Julian-Baumeler/marmot/website/figures/emb-036.png

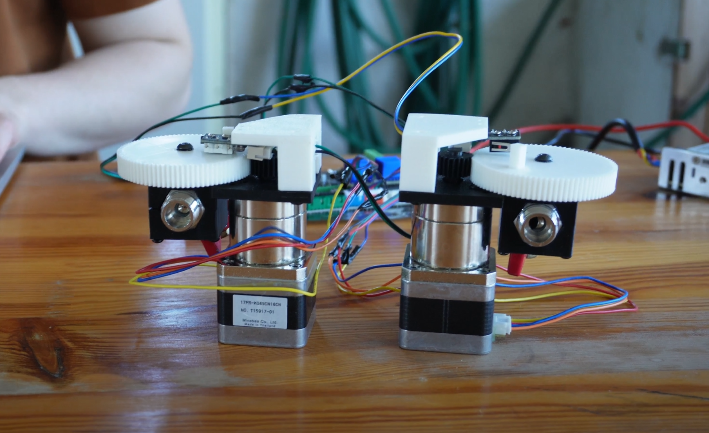
website/figures/emb-036.png
