Julian-Baumeler/marmot/website/figures/emb-038.png

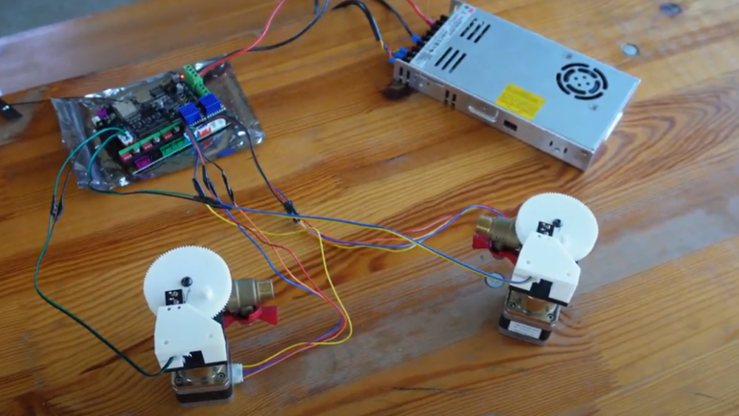
website/figures/emb-038.png
