Julian-Baumeler/marmot/website/figures/emb-051.png

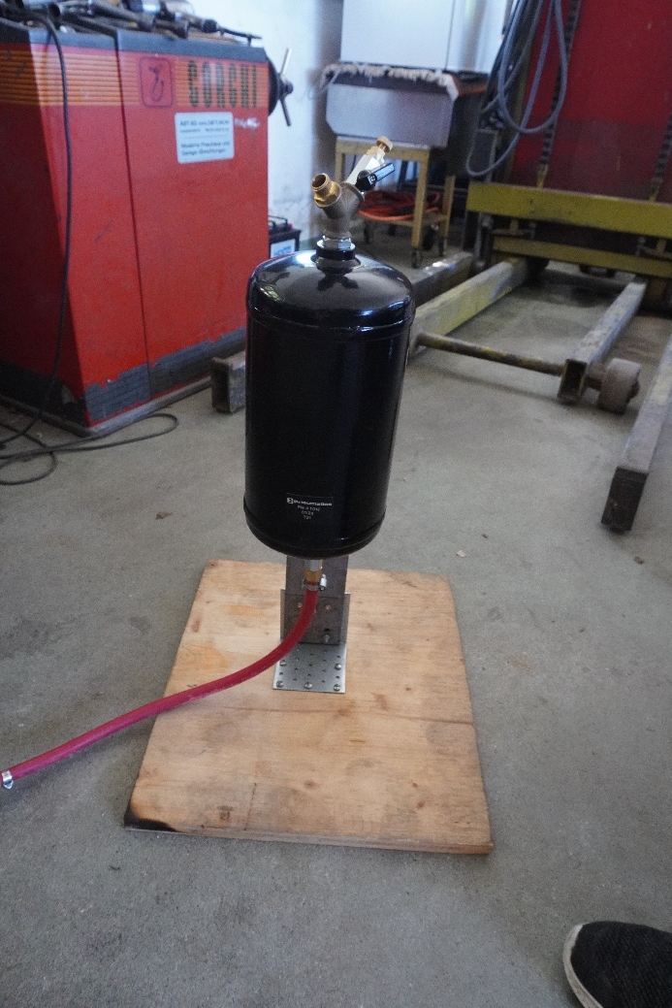
website/figures/emb-051.png
