Julian-Baumeler/marmot/website/models/Engine2-preview.png

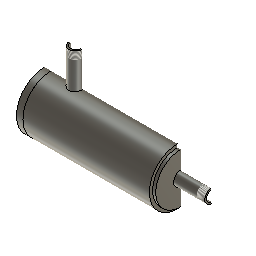
website/models/Engine2-preview.png
