Julian-Baumeler/marmot/website/models/Engine-preview.png

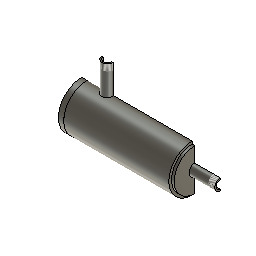
website/models/Engine-preview.png
