Julian-Baumeler/marmot/website/posters/06-mf-6.jpg

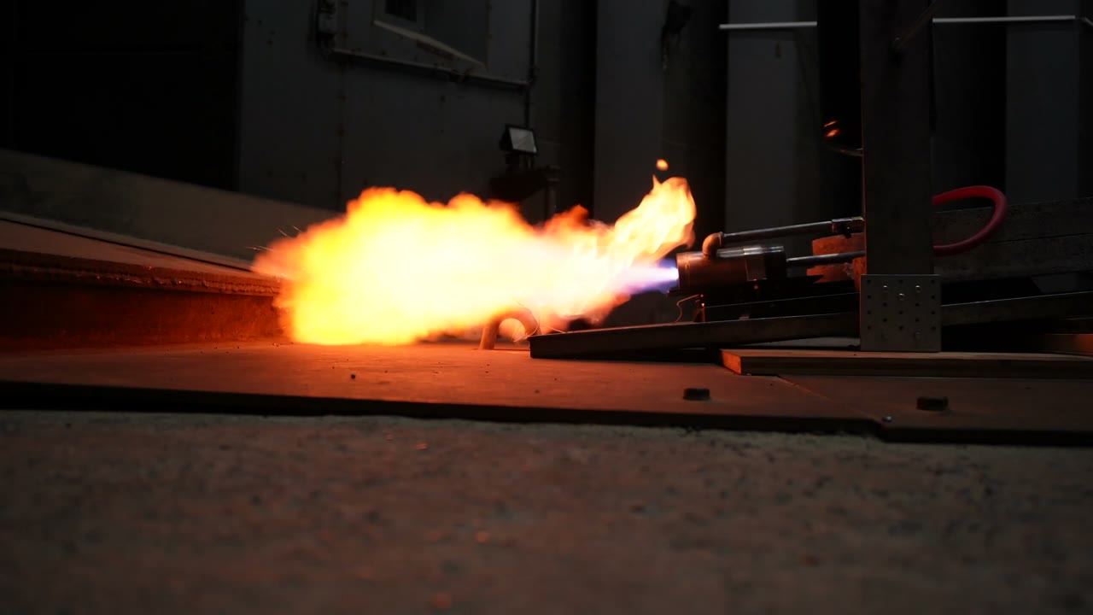
website/posters/06-mf-6.jpg
