Julian-Baumeler/marmot/website/posters/06-mf-6a.jpg

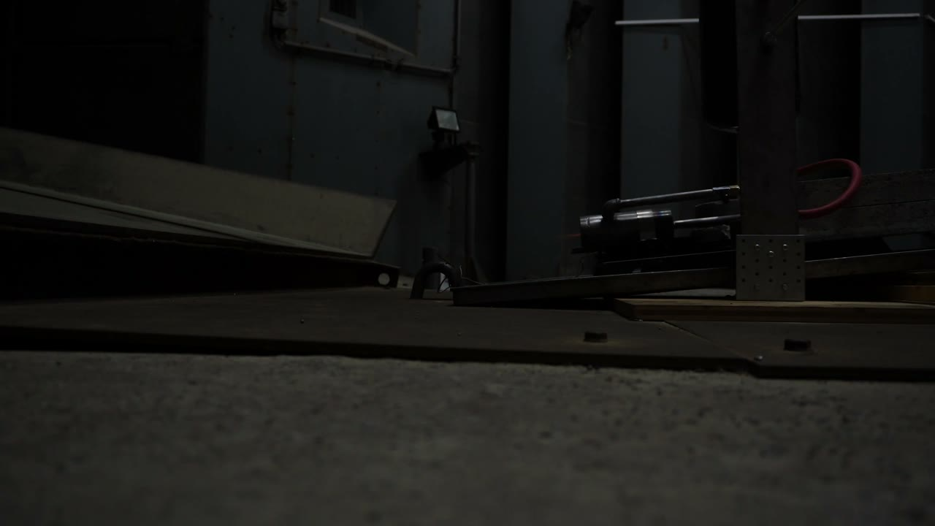
website/posters/06-mf-6a.jpg
