Julian-Baumeler/marmot/website/posters/06-mf-6b.jpg

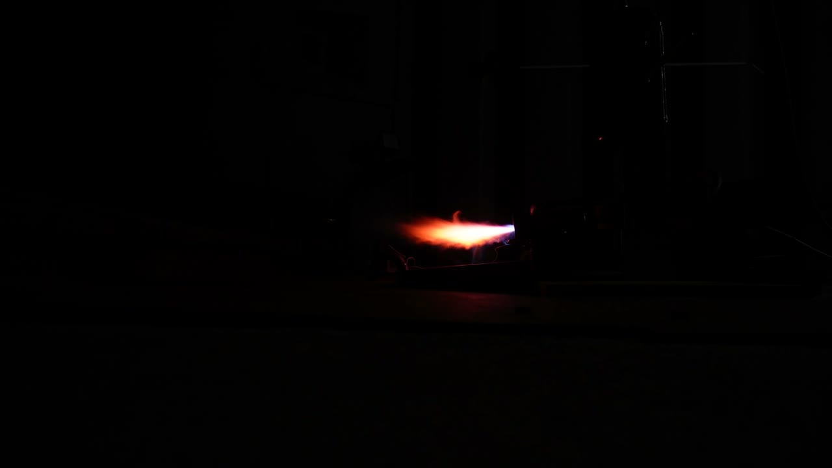
website/posters/06-mf-6b.jpg
