Julian-Baumeler/marmot/website/posters/06-mf-6c.jpg

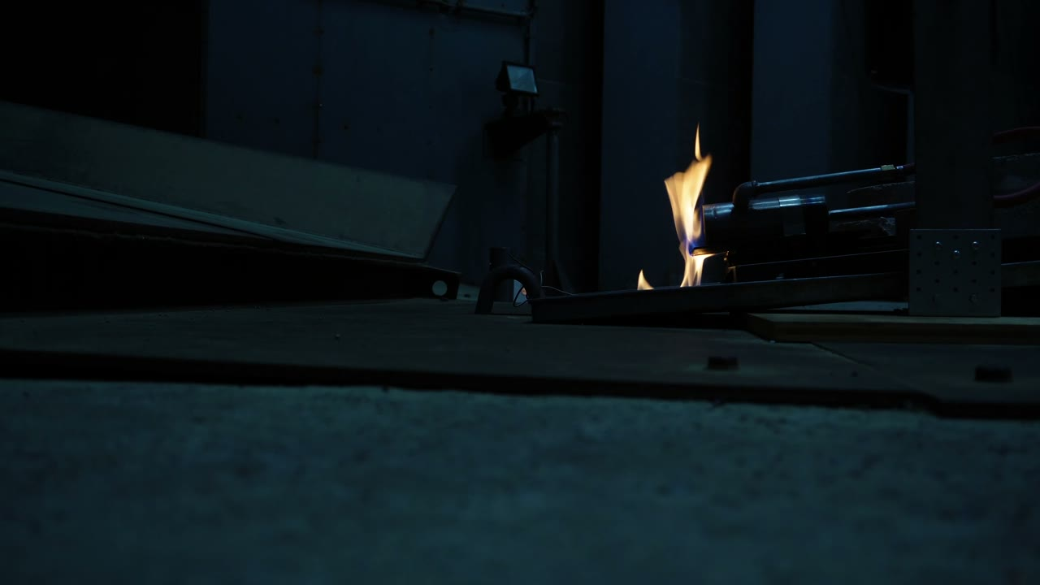
website/posters/06-mf-6c.jpg
