Julian-Baumeler/marmot/website/slides-gfx/engine-rich.jpg

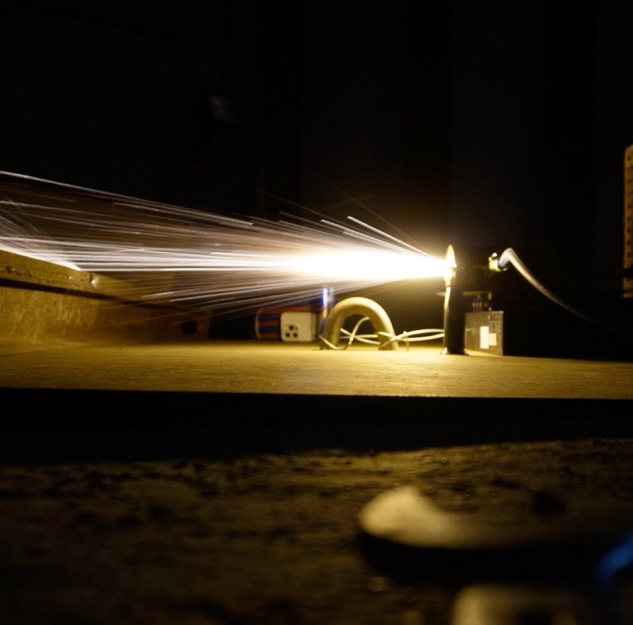
website/slides-gfx/engine-rich.jpg
