Julian-Baumeler/marmot/website/slides-gfx/kaltgas.jpg

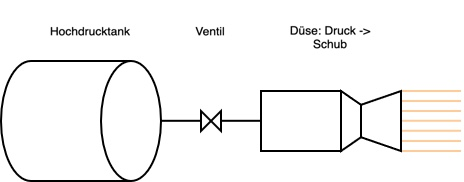
website/slides-gfx/kaltgas.jpg
