Julian-Baumeler/marmot/website/slides-gfx/kosten.jpg

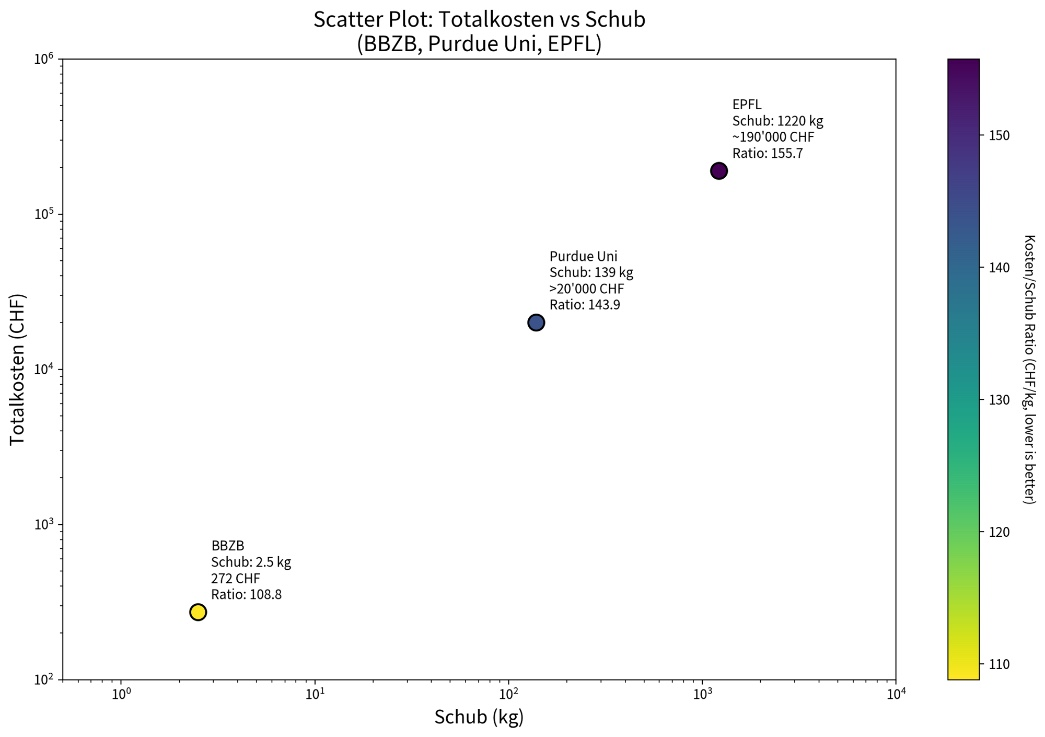
website/slides-gfx/kosten.jpg
