Julian-Baumeler/marmot/website/slides-gfx/mf5.jpg

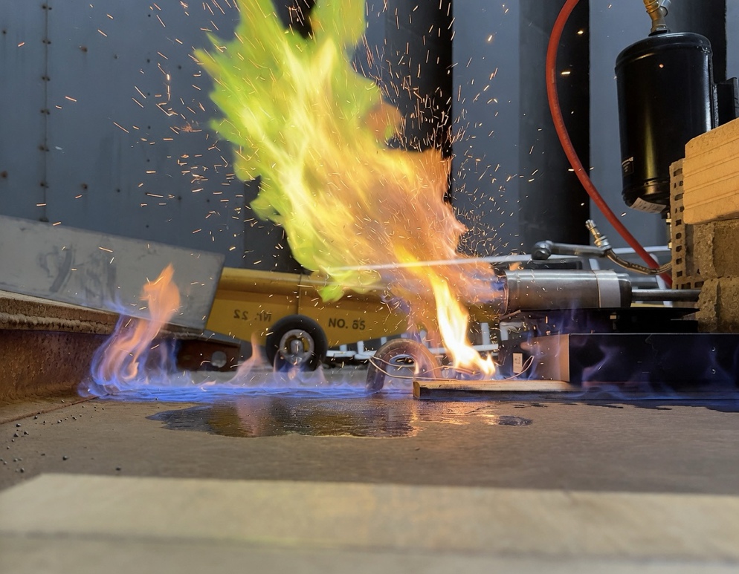
website/slides-gfx/mf5.jpg
