Julian-Baumeler/marmot/website/slides-gfx/mf7.jpg

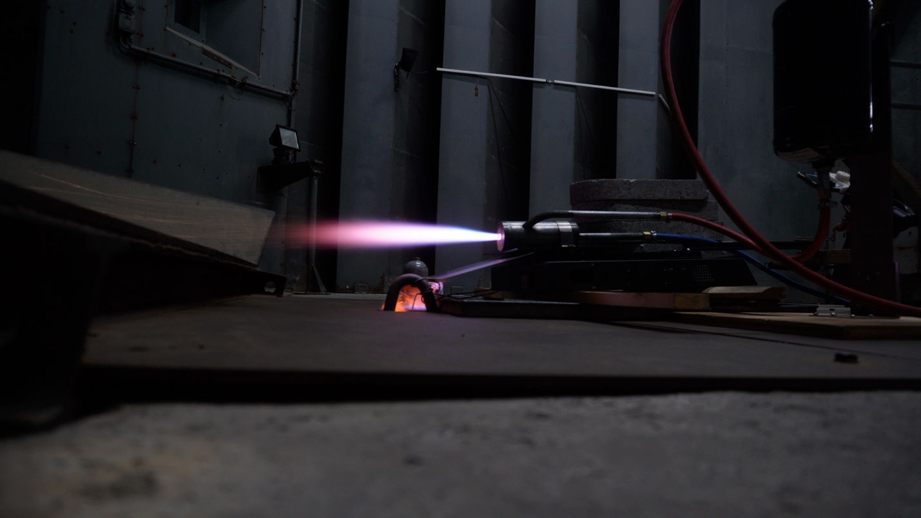
website/slides-gfx/mf7.jpg
