Julian-Baumeler/marmot/website/slides-gfx/qr-rocketengine.png

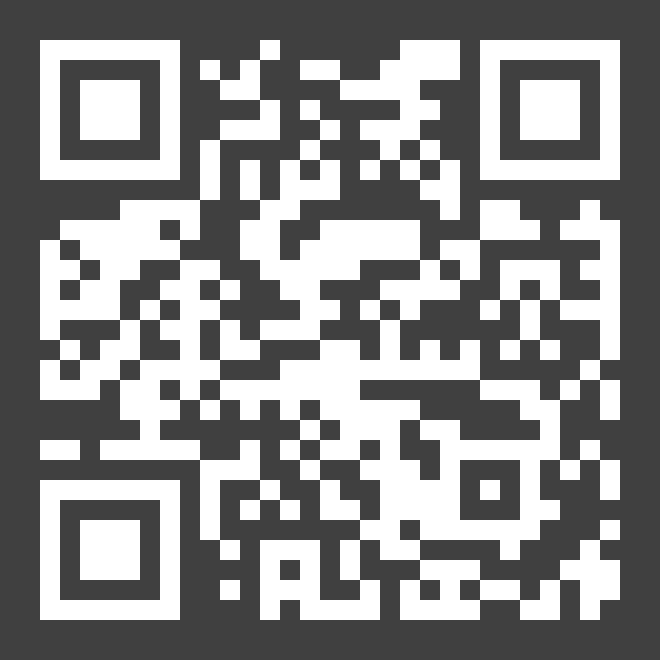
website/slides-gfx/qr-rocketengine.png
