Julian-Baumeler/marmot/website/slides-gfx/schub-feder.jpg

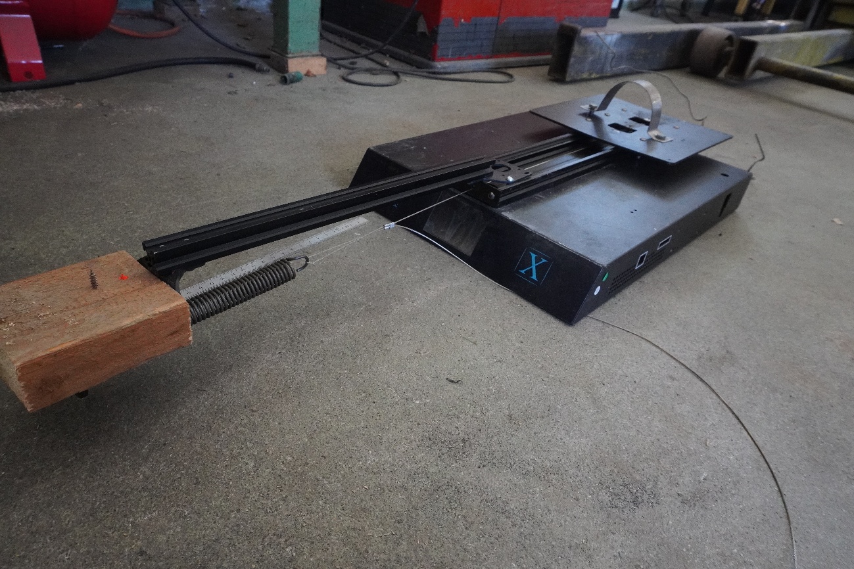
website/slides-gfx/schub-feder.jpg
