Julian-Baumeler/marmot/website/slides-gfx/turbopumpe.jpg

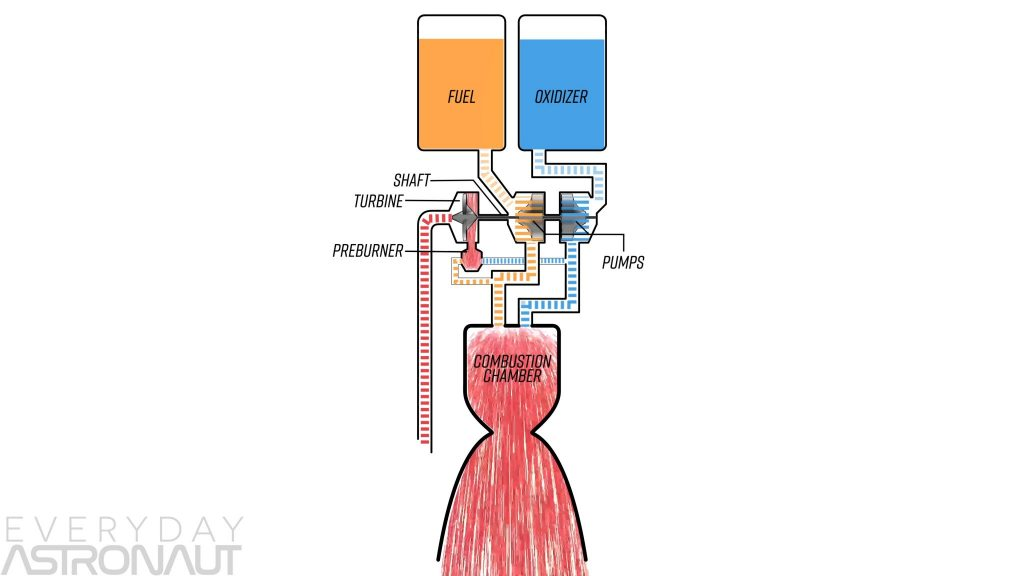
website/slides-gfx/turbopumpe.jpg
