Julian-Baumeler/marmot/website/slides-gfx/yg1.jpg

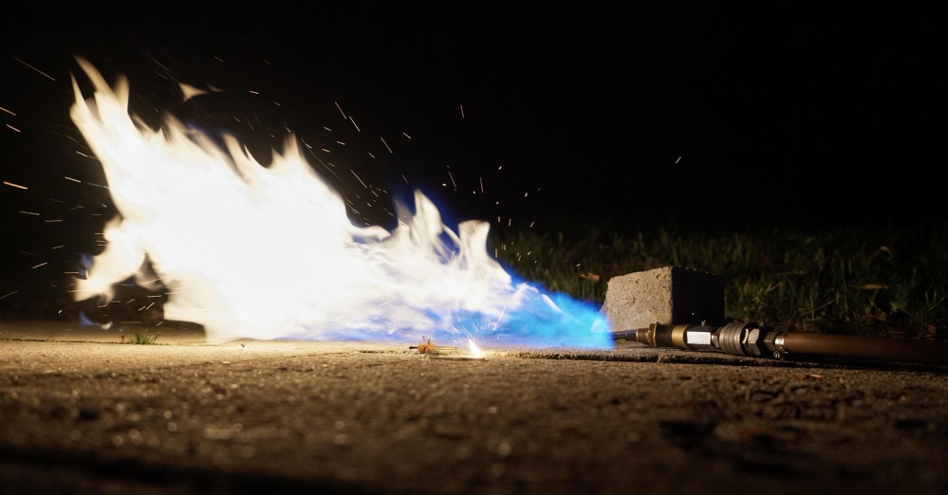
website/slides-gfx/yg1.jpg
